mlab-modules/GLCD01/doc/gen/dxf/GLCD01-F_Adhesive.dxf

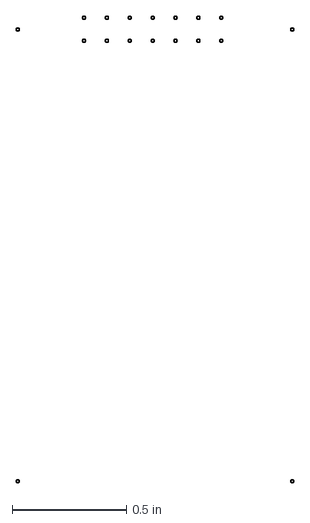
[picture p13: CAD file, 2026-05-16]
doc/gen/dxf/GLCD01-F_Adhesive.dxf
1.21 x 2.04 in
